SurajSonawane2415/MazeBlaze/Firmware/components/include/mazeblaze3.h

//contains all the header files to be used 
#ifndef MAZEBLAZE3_H
#define MAZEBLAZE3_H

#include <stdio.h>
#include <math.h>
#include "freertos/FreeRTOS.h"
#include "freertos/task.h"
#include "lsa.h" 
#include "motor_driver.h"
#include "pin_defs.h"
#include "line_following.h"
#include "rotary_encoder.h"
#include "spiffs_config.h"

#endif
